phamvettung/uninterruptible-power-supply/assets/real_time_trend2.PNG

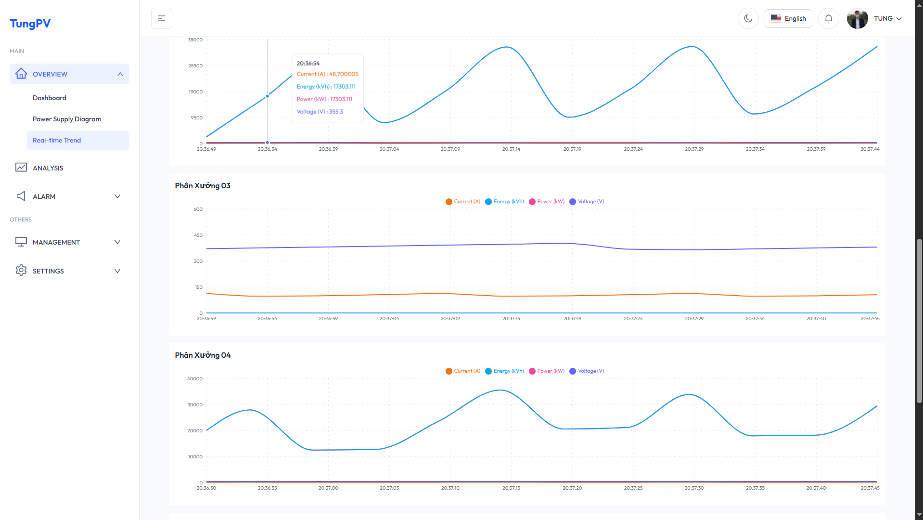
assets/real_time_trend2.PNG
