phamvettung/uninterruptible-power-supply/assets/state.PNG

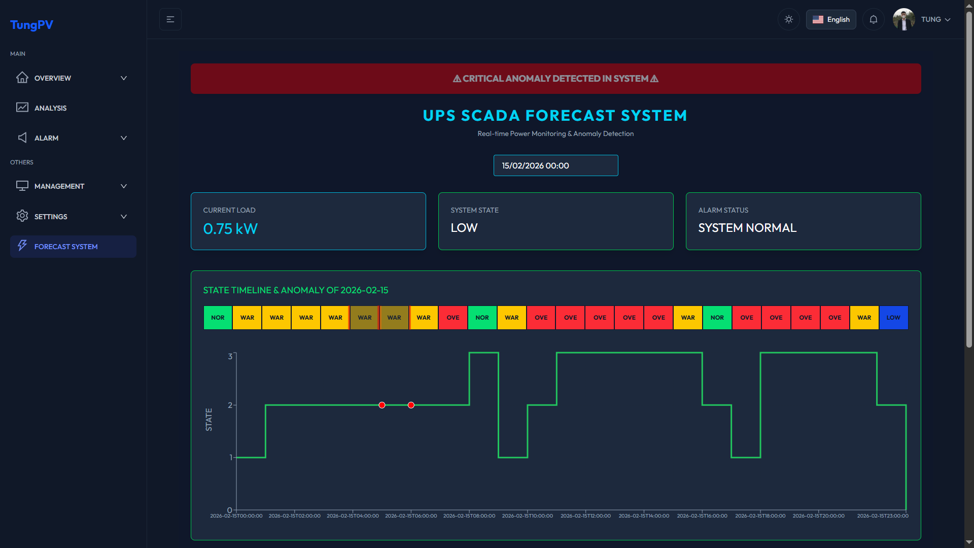
assets/state.PNG
